jorgis857/sistema-alerta-temprana-riesgo-hidrico/wiki/09-Equipo-Roles.md

[⬅ Volver al índice](00-Home.md)

# 9. Equipo de trabajo: roles, actividades y contribuciones

## 9.1 Integrantes — Equipo 2

| Integrante | Rol principal | Correo / contacto |
|---|---|---|
| **Mateo Ramírez Cabrera** | Hardware e integración de sensores | mateoraca@unisabana.edu.co |
| **Antonio Benítez Rueda** | Firmware y lógica de fusión de datos | antonioberu@unisabana.edu.co |
| **Jorge Andrés Rodríguez Huertas** | Documentación, pruebas y gestión del proyecto | jorgerohu@unisabana.edu.co |

---

## 9.2 Descripción de roles y contribuciones

### Mateo Ramírez Cabrera — Hardware e integración de sensores

- Selección y dimensionamiento de los sensores utilizados en WREWS: BME280, sensor ultrasónico OKY3261/HC-SR04 e INA219 con mini panel fotovoltaico.
- Diseño del esquema inicial de conexión en Wokwi (`diagram.json`): mapeo de pines del ESP32, bus I²C compartido y conexión de los actuadores.
- Diseño y verificación de los *custom chips* de Wokwi (`bme280custom`, `ina219custom`, `solarpanel`) utilizados para simular el comportamiento de los sensores.
- Integración física de los sensores y actuadores con el ESP32.
- Participación en las pruebas y calibración del sensor ultrasónico para la medición del nivel.
- Participación en la construcción y ajuste de la maqueta utilizada para representar diferentes niveles de almacenamiento.
- Verificación del funcionamiento del BME280, INA219, panel fotovoltaico, LCD 16×2 I²C, LEDs y buzzer.
- Documentación del hardware y del esquema general de integración en la Wiki.

### Antonio Benítez Rueda — Firmware y lógica de fusión de datos

- Desarrollo y ajuste del firmware embebido para el ESP32.
- Implementación de la lectura de sensores mediante I²C y GPIO.
- Implementación del cálculo de nivel, VPD, irradiancia estimada, índice evaporativo, tasa de descenso e índice de riesgo hídrico.
- Implementación de la máquina de estados de alerta (`NORMAL`, `PRECAUCIÓN` y `CRÍTICO`) y de las reglas de seguridad independientes al promedio ponderado.
- Adaptación de la interfaz de visualización para la **LCD 16×2 I²C** utilizada en el prototipo físico.
- Implementación y ajuste del control de LEDs y buzzer.
- Participación en la calibración y depuración del prototipo físico.
- Apoyo en la construcción de los diagramas UML a partir de la arquitectura y lógica implementadas.

### Jorge Andrés Rodríguez Huertas — Documentación, pruebas y gestión del proyecto

- Redacción y estructuración de la Wiki técnica conforme a los requisitos del Challenge #1.
- Diseño y organización del protocolo de pruebas y de su autoevaluación.
- Verificación matemática independiente de los resultados y fórmulas utilizadas durante la etapa de simulación.
- Elaboración del modelo de negocio.
- Coordinación general del equipo y gestión del repositorio de GitHub.
- Documentación de los resultados obtenidos con el prototipo físico.
- Organización de la presentación final del proyecto.
- Preparación del guion y coordinación del video de demostración de WREWS.

---

## 9.3 Trabajo colaborativo

Aunque cada integrante contó con un rol principal, la integración final del proyecto requirió trabajo conjunto.

Entre las actividades realizadas colaborativamente se encuentran:

- definición de la problemática y alcance del sistema;
- selección de sensores y actuadores;
- definición de los estados de alerta;
- discusión de los pesos y umbrales de la lógica de riesgo;
- pruebas en Wokwi;
- integración del circuito físico;
- calibración del sensor de nivel;
- construcción y ajuste de la maqueta;
- validación de los estados NORMAL, PRECAUCIÓN y CRÍTICO;
- revisión de la documentación;
- preparación y grabación del video final.

El proyecto siguió un proceso iterativo en el que los resultados obtenidos durante la simulación y las pruebas físicas llevaron a realizar ajustes en el firmware, la calibración y la documentación.

---

## 9.4 Acta de reunión y evaluación del equipo

| Campo | Detalle |
|---|---|
| **Proyecto** | WREWS — Water Risk Early Warning System — Challenge #1 |
| **Curso** | Internet de las Cosas — 2026-2 — Universidad de La Sabana |
| **Fecha de la reunión** | 20/08/2026 |
| **Asistentes** | Mateo Ramírez Cabrera, Antonio Benítez Rueda, Jorge Andrés Rodríguez Huertas |
| **Modalidad** | Presencial |

### Temas tratados

1. Revisión del alcance del reto y de las restricciones técnicas del enunciado.
2. Validación del modelo de fusión de datos basado en nivel, condiciones ambientales y tasa de descenso.
3. Distribución de roles y actividades entre los tres integrantes.
4. Revisión de los resultados obtenidos durante las pruebas en Wokwi.
5. Planeación de la integración del prototipo físico.
6. Calibración y pruebas del sistema completo.
7. Planeación de la sustentación y del video de demostración.

### Compromisos y evaluación de participación

| Integrante | Compromiso adquirido | Cumplimiento | Observaciones |
|---|---|---|---|
| Mateo Ramírez Cabrera | Integrar el hardware, sensores y componentes necesarios para la medición y actuación del sistema | ✅ Cumplido | Participó además en calibración, maqueta y pruebas físicas |
| Antonio Benítez Rueda | Entregar y ajustar el firmware con lógica de fusión y estados de alerta | ✅ Cumplido | El firmware fue adaptado y probado sobre el prototipo físico |
| Jorge Andrés Rodríguez Huertas | Completar la documentación, protocolo de pruebas y organización del repositorio | ✅ Cumplido | Participó además en resultados, presentación y video final |

---

## 9.5 Autoevaluación de la contribución individual

Autoevaluación del equipo frente al indicador **“Contribuir al desarrollo de las actividades propias del rol asignado dentro del equipo de trabajo”**, utilizando la escala de la rúbrica del curso: **Novato / Aprendiz / Bueno / Experto**.

| Integrante | Nivel autoevaluado | Justificación breve |
|---|---|---|
| Mateo Ramírez Cabrera | **Experto** | Cumplió su responsabilidad de integración de hardware y sensores, participó en la simulación, montaje físico, calibración y validación funcional del prototipo. |
| Antonio Benítez Rueda | **Experto** | Desarrolló y ajustó el firmware, implementó la lógica de fusión y los estados de alerta y participó en la depuración del sistema físico. |
| Jorge Andrés Rodríguez Huertas | **Experto** | Estructuró la documentación, protocolo de pruebas y repositorio, verificó los resultados y coordinó la preparación de la entrega y presentación final. |

---

## 9.6 Resultado del trabajo del equipo

La distribución de responsabilidades y el trabajo colaborativo permitieron desarrollar el proyecto de manera progresiva:

```text
PROBLEMÁTICA
     ↓
DISEÑO
     ↓
SIMULACIÓN EN WOKWI
     ↓
DESARROLLO DEL FIRMWARE
     ↓
INTEGRACIÓN DEL HARDWARE
     ↓
CONSTRUCCIÓN DE LA MAQUETA
     ↓
CALIBRACIÓN
     ↓
PRUEBAS FÍSICAS
     ↓
DOCUMENTACIÓN Y VIDEO
     ↓
WREWS
```

El resultado final es un **prototipo físico funcional** capaz de adquirir múltiples variables, procesarlas localmente y generar una alerta temprana de riesgo hídrico mediante tres estados de fácil interpretación.

---

## 9.7 Contribuciones en el Challenge #2

Roles definidos en la hoja de trabajo del Challenge #2:

| Integrante | Rol | GitHub |
|---|---|---|
| **Mateo Ramírez Cabrera** | Hardware, integración en carcasa, alimentación, montaje y edición de video | [technologybyteo](https://github.com/technologybyteo) |
| **Antonio Benítez Rueda** | Firmware: FreeRTOS, fusión, servidor web y tablero | [antobeni07](https://github.com/antobeni07) |
| **Jorge Andrés Rodríguez Huertas** | Banco de pruebas, calibración, Wiki, video y gestión (actas) | [jorgis857](https://github.com/jorgis857) |

### Mateo Ramírez Cabrera — Hardware, carcasa e integración

- Diseño de la carcasa en CadQuery (iteraciones v11 a v17) y su impresión en PETG: caja, tapa, piso intermedio, techo ventilado del BME280 y acople al tubo de PVC.
- Integración de los componentes en la carcasa y del sensor de nivel en el tubo de PVC.
- Diseño de la alimentación por pilas con interruptor y distribución de las filas de 5 V y 3.3 V.
- Edición del video de demostración.
- ⟨completar⟩

### Antonio Benítez Rueda — Firmware, modelo y tablero de control

- Firmware v6: modelo de evaporación de Priestley-Taylor con FAO-56, ventana móvil, pesos AHP, nuevos umbrales y autotest de referencia.
- Firmware v7: tareas de FreeRTOS con mutex, Wi-Fi en modo estación con reconexión y dos redes, servidor web embebido, inicio de sesión, tablero con histórico, eventos y silencio de la alarma, y calibración desde el tablero guardada en flash.
- Diagnóstico y corrección de las fallas encontradas en las pruebas (tono del buzzer, recuperación del tablero, saturación del índice con sol, falsos positivos por evaporación).
- Hojas de referencias del modelo de evaporación y de pesos y umbrales ⟨confirmar autoría⟩.
- ⟨completar⟩

### Jorge Andrés Rodríguez Huertas — Pruebas, documentación y video

- Diseño y ejecución del banco de pruebas y de la calibración de sensores del Challenge #2.
- Actualización de la Wiki.
- Participación en el video de demostración.
- Gestión del proyecto y actas de reunión.
- ⟨completar⟩

### Acta de reunión del Challenge #2

| Campo | Detalle |
|---|---|
| **Proyecto** | WREWS — Water Risk Early Warning System — Challenge #2 |
| **Fecha de la reunión** | ⟨completar⟩ |
| **Asistentes** | ⟨completar⟩ |
| **Modalidad** | ⟨completar⟩ |
| **Temas tratados** | ⟨completar: p. ej. retroalimentación del Challenge #1, decisiones de pesos y umbrales, arquitectura del tablero, pruebas y video⟩ |
| **Compromisos y cumplimiento** | ⟨completar⟩ |

### Autoevaluación de la contribución individual (Challenge #2)

| Integrante | Nivel autoevaluado | Justificación breve |
|---|---|---|
| Mateo Ramírez Cabrera | ⟨completar⟩ | ⟨completar⟩ |
| Antonio Benítez Rueda | ⟨completar⟩ | ⟨completar⟩ |
| Jorge Andrés Rodríguez Huertas | ⟨completar⟩ | ⟨completar⟩ |

---

[⬅ Anterior: Uso de Inteligencia Artificial](08-Uso-de-IA.md) · [⬆ Índice](00-Home.md) · [Siguiente: Resumen ejecutivo en inglés ➡](10-English-Executive-Summary.md)
